ErickRdgz/Sistema-IoT-para-monitoreo-de-servidores/App/camera_pi.py

import io
import time
import picamera
from base_camera import BaseCamera


class Camera(BaseCamera):
    @staticmethod
    def frames():
        with picamera.PiCamera() as camera:
            # let camera warm up
            time.sleep(2)
            # camera.rotation=180
            camera.resolution = (640,480)

            stream = io.BytesIO()
            for _ in camera.capture_continuous(stream, 'jpeg',
                                                 use_video_port=True):
                # return current frame
                stream.seek(0)
                yield stream.read()

                # reset stream for next frame
                stream.seek(0)
                stream.truncate()
